SchaafR/IAbeille/test/testMicro/testMicro.ino

#include "driver/i2s.h"

#define I2S_WS  42
#define I2S_SD  41
#define I2S_SCK -1   // pas utilisé en PDM

void setup() {
  Serial.begin(115200);

  i2s_config_t i2s_config = {
    .mode = (i2s_mode_t)(I2S_MODE_MASTER | I2S_MODE_RX | I2S_MODE_PDM),
    .sample_rate = 16000,
    .bits_per_sample = I2S_BITS_PER_SAMPLE_16BIT,
    .channel_format = I2S_CHANNEL_FMT_ONLY_LEFT,
    .communication_format = I2S_COMM_FORMAT_STAND_I2S,
    .intr_alloc_flags = 0,
    .dma_buf_count = 8,
    .dma_buf_len = 64,
    .use_apll = false
  };

  i2s_pin_config_t pin_config = {
    .bck_io_num = -1,
    .ws_io_num = I2S_WS,
    .data_out_num = -1,
    .data_in_num = I2S_SD
  };

  i2s_driver_install(I2S_NUM_0, &i2s_config, 0, NULL);
  i2s_set_pin(I2S_NUM_0, &pin_config);
}

void loop() {
  int16_t sample;
  size_t bytes_read;

  i2s_read(I2S_NUM_0, &sample, sizeof(sample), &bytes_read, portMAX_DELAY);

  if (bytes_read > 0) {
    Serial.println(sample);
  }
}
