SchaafR/IAbeille/test/testQueen/sound_lib/src/sound_lib.h

#ifndef FRELON_INFERENCE_H
#define FRELON_INFERENCE_H

#include "model-parameters/model_metadata.h"
#include "edge-impulse-sdk/classifier/ei_run_classifier.h"

// Doit contenir les deux handles
extern ei_impulse_handle_t impulse_handle_938676_1;
extern ei_impulse_handle_t impulse_handle_943803_2;

#endif
